jarevalob0/Control-Flujo-de-Agua/Diagramas/DiagramaTecnologico.jpeg

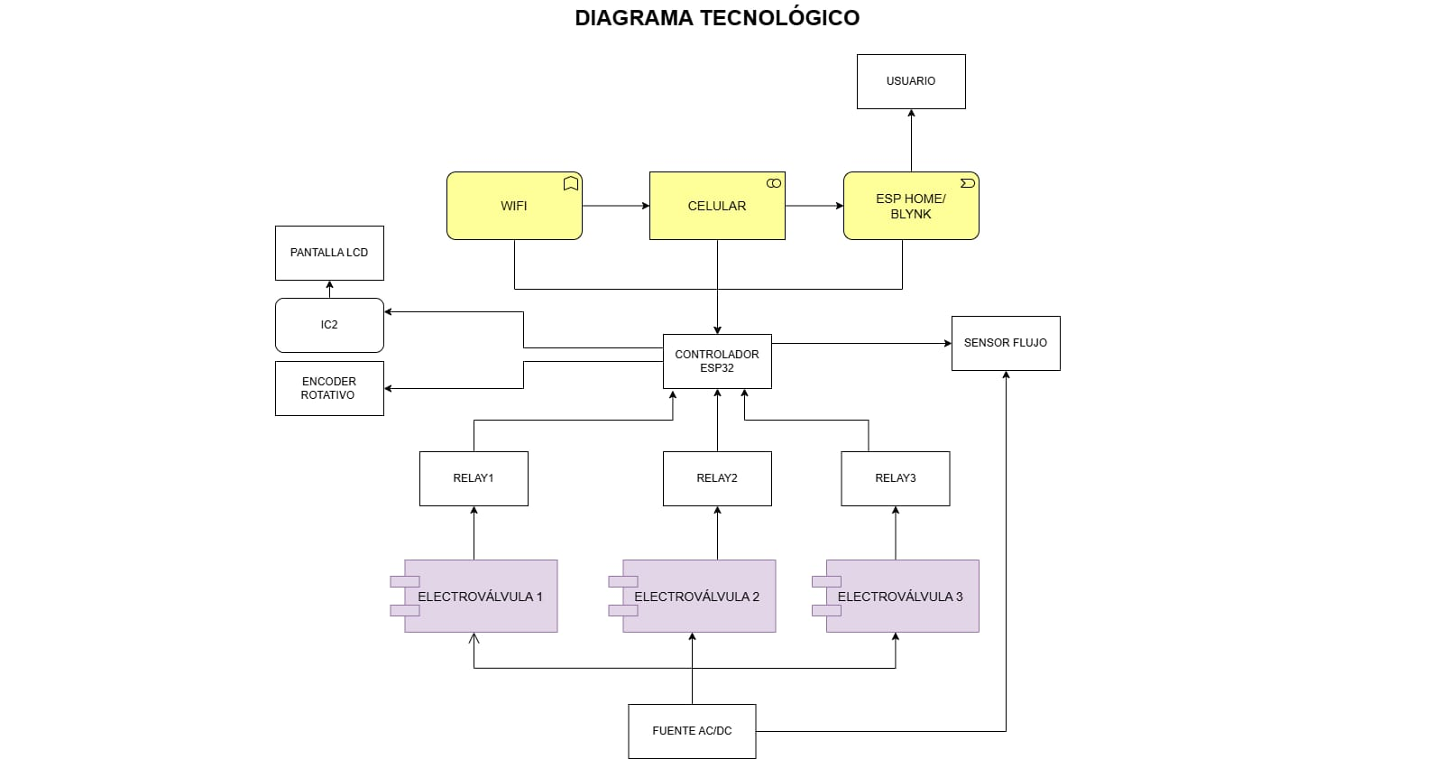
Diagramas/DiagramaTecnologico.jpeg
