jarevalob0/Control-Flujo-de-Agua/Evidencias/Foto2.jpeg

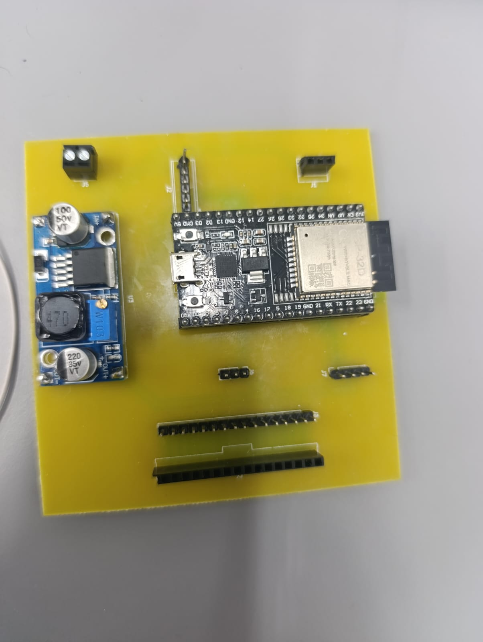
Evidencias/Foto2.jpeg
