jarevalob0/Control-Flujo-de-Agua/Evidencias/Foto6.jpeg

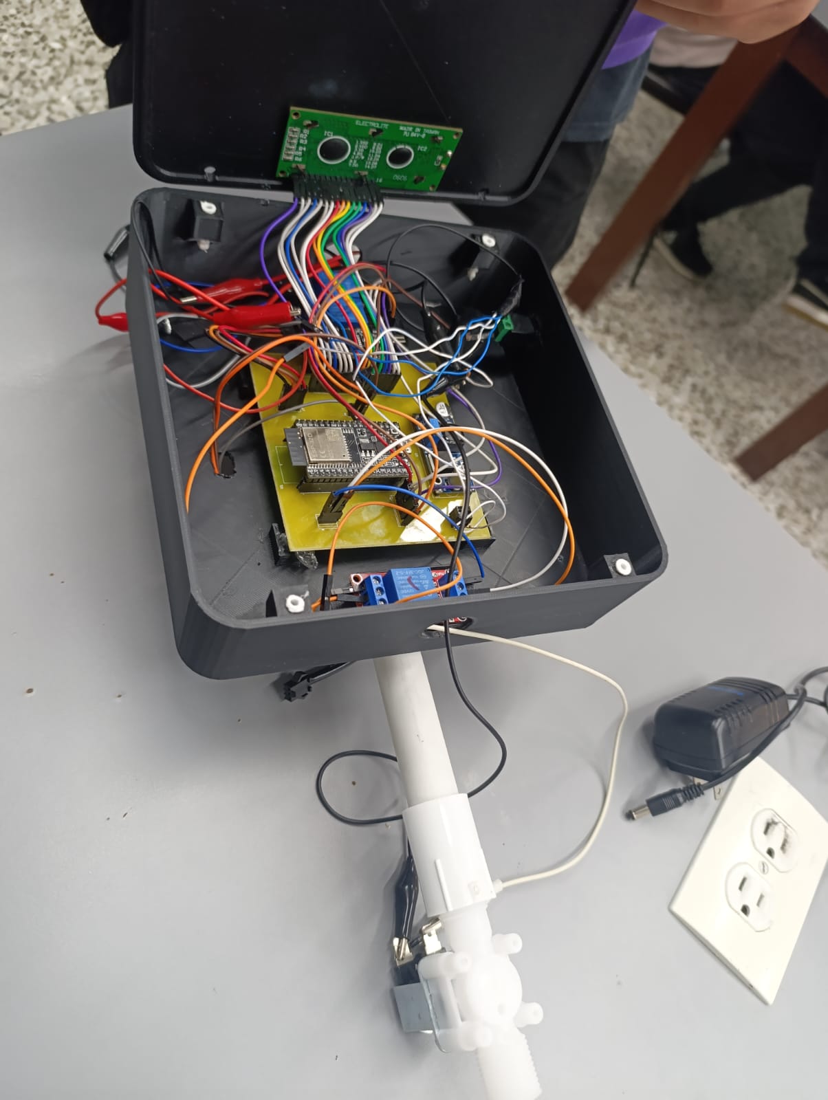
Evidencias/Foto6.jpeg
