jarevalob0/Control-Flujo-de-Agua/Evidencias/Foto7.jpeg

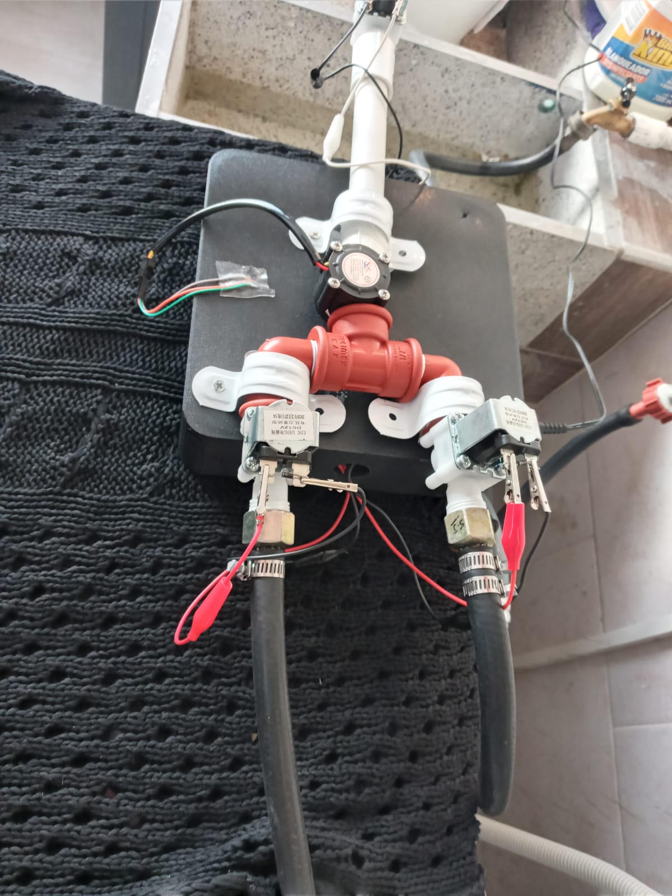
Evidencias/Foto7.jpeg
